bones384/ESP32S3SmartCalendar/components/arduino/variants/cytron_maker_feather_aiot_s3/partitions-8MB-tinyuf2.csv

# ESP-IDF Partition Table
# Name | Type | SubType | Offset | Size | Flags
# bootloader.bin |  | 0x1000 | 32K
# partition table |  | 0x8000 | 4K
nvs | data | nvs | 0x9000 | 20K
otadata | data | ota | 0xe000 | 8K
ota_0 | 0 | ota_0 | 0x10000 | 2048K
ota_1 | 0 | ota_1 | 0x210000 | 2048K
uf2 | app | factory | 0x410000 | 256K
ffat | data | fat | 0x450000 | 3776K
